hyelie/keyboard/housing/result/right plate.step

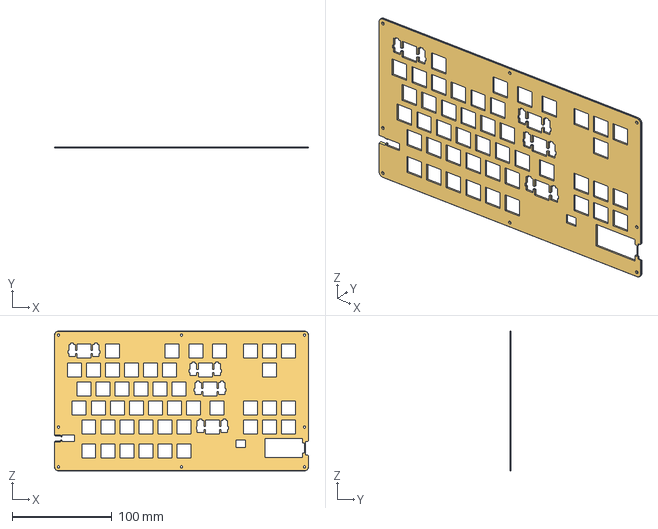
[picture p36: CAD file, 2023-09-01]
housing/result/right plate.step
254.3 x 1.50 x 140.0 mm
