hyelie/keyboard/housing/result/left bottom plate.step

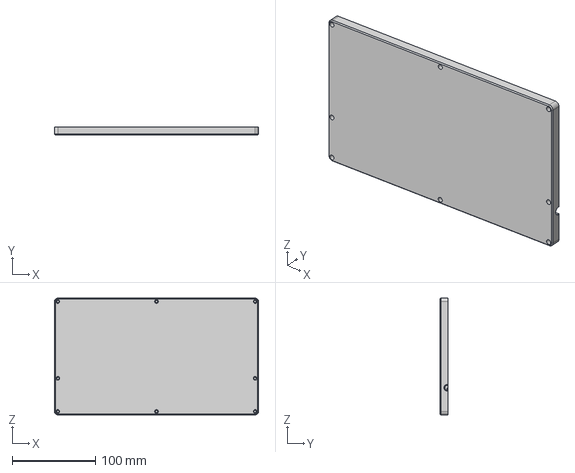
[picture p37: CAD file, 2023-09-01]
housing/result/left bottom plate.step
244.8 x 9.60 x 140.0 mm
