hyelie/keyboard/housing/result/right copy - relocated screw holes v2.step

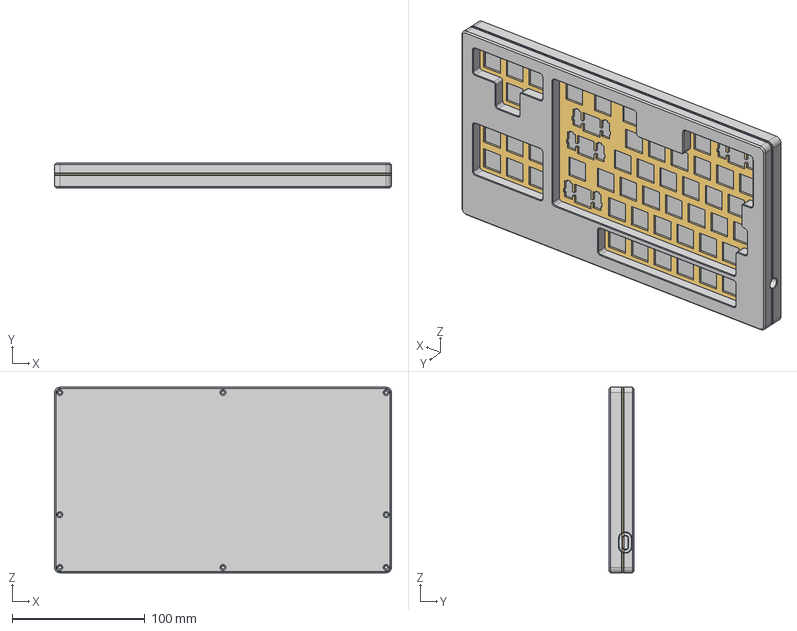
[picture p38: CAD file, 2023-09-01]
housing/result/right copy - relocated screw holes v2.step
254.3 x 18.6 x 140.0 mm
plate
top plate
bottom plate
