hyelie/keyboard/housing/result/left copy - relocated screw holes v2.step

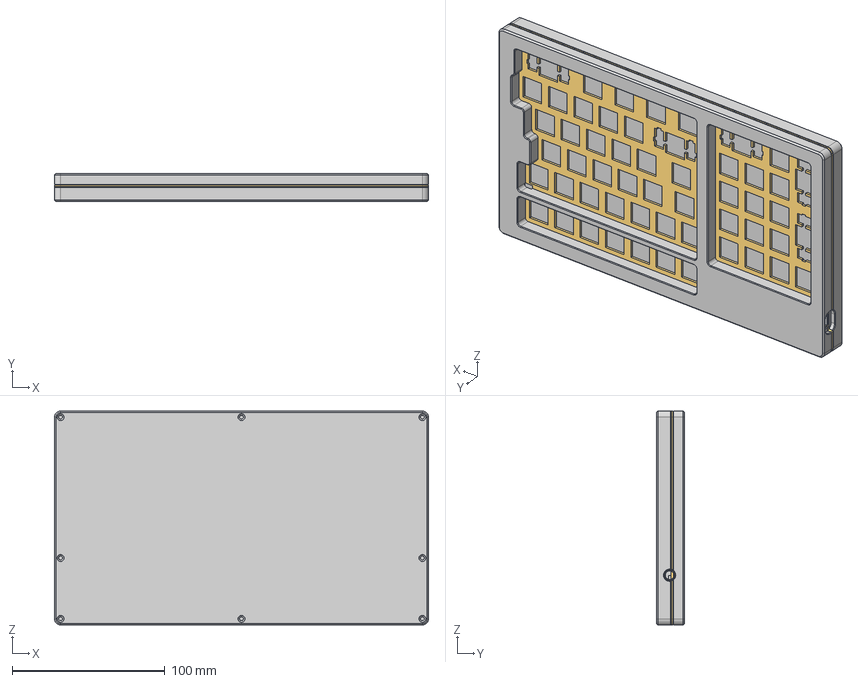
[picture p39: CAD file, 2023-09-01]
housing/result/left copy - relocated screw holes v2.step
244.8 x 18.6 x 140.0 mm
plate
top plate
bottom plate
